malek-luky/IoT-Prototyping/3D Model/v4/Button.obj

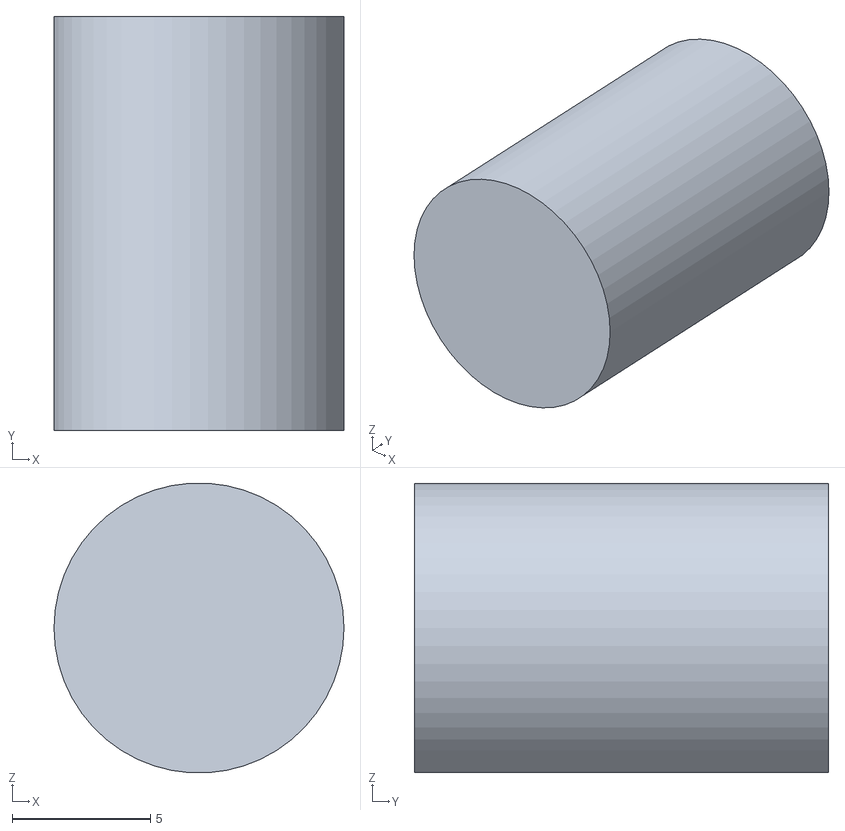
[picture p20: CAD file, 2023-11-23, an earlier design]
3D Model/v4/Button.obj
10.5 x 15.0 x 10.5
