malek-luky/IoT-Prototyping/3D Model/v3/UM3E_Inside.3mf

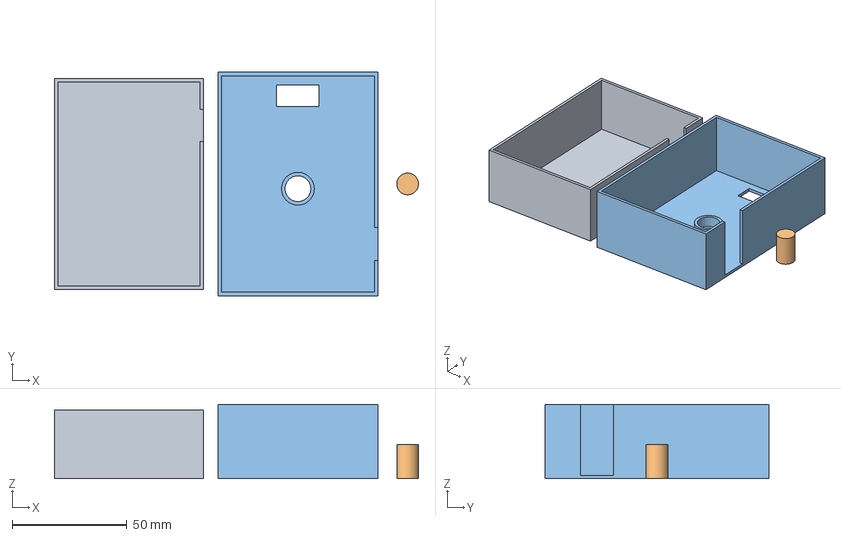
[picture p21: CAD file, 2023-11-23, an earlier design]
3D Model/v3/UM3E_Inside.3mf
158.9 x 97.6 x 32.5 mm
Inside.obj
Button.obj
Outside.obj
