malek-luky/IoT-Prototyping/3D Model/v4/UM3E_Inside.3mf

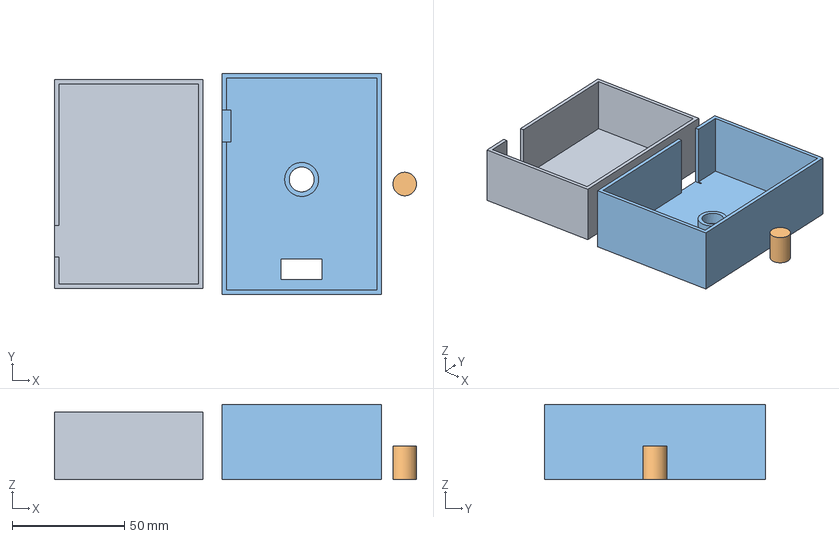
[picture p22: CAD file, 2023-11-23, an earlier design]
3D Model/v4/UM3E_Inside.3mf
161.0 x 98.2 x 33.4 mm
Inside.obj
Button.obj
Outside.obj
